razanskylab/Cascade_Trigger/board_firmware/TeensyTrigger 2.1/include/serial_lib.h

#ifndef SERIAL_LIB
#define SERIAL_LIB

#include <Arduino.h> // always required when using platformio

uint16_t serial_read_16bit();
uint16_t serial_read_16bit_no_wait();
uint32_t serial_read_32bit();

void serial_write_16bit(uint16_t writeData);
void serial_write_32bit(uint16_t writeData);
void serial_wait_next_command();
void serial_wait_four_bytes();

#endif
